ZeshuLiu/esp32_keyboard/Keyboard_code/poker_keyboard/poker_keyboard.h

#ifndef ESP_KEYBOARD_H
#define ESP_KEYBOARD_H
#include "Layout.h"
#include "L_CH932x.h"

bool DBG_KEYBOARD = 1;

#ifdef Joker
# define DeviceName "Joker_60" //设备名
#endif

#ifdef MasterYoda
# define DeviceName "MasterYoda"
#endif

# define Manufacturer "Liu"        //设备制造商
# define DevicePower 100             //电量

int DFT_BOOT_MODE; //0是usb，1是蓝牙


//I2C总线信息
# define kbd_SDA 21
# define kbd_SCL 22

#ifdef Joker
#ifdef Ver2
L_CH9329 ch9329;
#endif
#endif


#endif
