ZeshuLiu/esp32_keyboard/Keyboard_code/poker_keyboard/Pic.h

static const unsigned char dog_bmp [] PROGMEM ={
0xFF,0xFF,0xFF,0xFF,0xFF,0xFF,0xFF,0xFF,0xFF,0xFF,0xFF,0xFF,0xFF,0xFF,0xFF,0xFF,
0xFF,0xFF,0xFF,0xFF,0xFF,0xFF,0xFF,0xFF,0xFF,0xFF,0xFF,0xFF,0xFF,0xFF,0xFF,0xFF,
0xFF,0xFF,0xFF,0xFF,0xFF,0xFF,0xFF,0xFF,0x09,0x00,0xFF,0xFF,0xFF,0xFF,0xFF,0xFF,
0xFF,0xFF,0xFF,0xFF,0xFF,0xFF,0xFF,0x3F,0x1F,0x00,0xF0,0xFF,0xFF,0xFF,0xFF,0xFF,
0xFF,0xFF,0xFF,0xFF,0xFF,0xFF,0xFF,0xC3,0xFF,0xFF,0xC2,0xFF,0xFF,0xFF,0xFF,0xFF,
0xFF,0xFF,0xFF,0xFF,0xFF,0xFF,0x7F,0xF8,0xFF,0xFF,0x0F,0xFF,0xFF,0xFF,0xFF,0xFF,
0xFF,0xFF,0xFF,0xFF,0xFF,0xFF,0x0F,0xFC,0xFF,0xFF,0x3F,0xFC,0xFF,0xFF,0xFF,0xFF,
0xFF,0xFF,0xFF,0xFF,0xFF,0xFF,0x07,0xFE,0xFF,0xFF,0xFF,0xF8,0xFF,0xFF,0xFF,0xFF,
0xFF,0xFF,0xFF,0xFF,0xFF,0xFF,0x27,0xFF,0xFF,0xFA,0xFF,0xC1,0xFF,0xFF,0xFF,0xFF,
0xFF,0xFF,0xFF,0xFF,0xFF,0xFF,0x93,0x7F,0x7F,0xF8,0xFF,0x87,0xFF,0xFF,0xFF,0xFF,
0xFF,0xFF,0xFF,0xFF,0xFF,0xFF,0xB3,0x7F,0x78,0xFC,0xFF,0x3D,0xFF,0xFF,0xFF,0xFF,
0xFF,0xFF,0xFF,0xFF,0xFF,0xFF,0x19,0x1F,0x7E,0xFE,0x9F,0x39,0xFF,0xFF,0xFF,0xFF,
0xFF,0xFF,0xFF,0xFF,0xFF,0xFF,0x09,0x5E,0x7C,0xF8,0x1F,0x20,0xFE,0xFF,0xFF,0xFF,
0xFF,0xFF,0xFF,0xFF,0xFF,0xFF,0xDD,0xDF,0x3E,0xC0,0x31,0xE0,0xFC,0xFF,0xFF,0xFF,
0xFF,0xFF,0xFF,0xFF,0xFF,0xFF,0xE6,0xFB,0x3F,0x00,0xE1,0xC0,0xE1,0xFF,0xFF,0xFF,
0xFF,0xFF,0xFF,0xFF,0xFF,0x7F,0x26,0xF8,0x3F,0x00,0xE0,0xF8,0xE3,0xFF,0xFF,0xFF,
0xFF,0xFF,0xFF,0xFF,0xFF,0x7F,0x17,0xFC,0x7F,0x00,0x30,0xE0,0xC7,0xFF,0xFF,0xFF,
0xFF,0xFF,0xFF,0xFF,0xFF,0x9F,0x17,0xF8,0xFF,0x40,0x31,0xCE,0x0F,0xFF,0xFF,0xFF,
0xFF,0xFF,0xFF,0xFF,0xFF,0x8F,0x23,0xC6,0xFF,0xF1,0x38,0xFC,0x3F,0xFC,0xFF,0xFF,
0xFF,0xFF,0xFF,0xFF,0xFF,0xDF,0xE7,0x81,0xFF,0xFF,0x10,0xFD,0x5F,0xF0,0xFF,0xFF,
0xFF,0xFF,0xFF,0xFF,0xFF,0xDF,0xE3,0x88,0xFF,0x7F,0x1E,0xFF,0x87,0xFF,0xFF,0xFF,
0xFF,0xFF,0xFF,0xFF,0xFF,0xCF,0x23,0x3E,0xFF,0x7F,0x3E,0xFE,0x1F,0xFE,0xFF,0xFF,
0xFF,0xFF,0xFF,0xFF,0xFF,0xCF,0x83,0x3F,0xFF,0x3F,0x1F,0xFC,0x3F,0xFF,0xFF,0xFF,
0xFF,0xFF,0xFF,0xFF,0xFF,0xCF,0xC3,0x69,0xFE,0x3F,0xBF,0xFD,0x7F,0xFE,0xFF,0xFF,
0xFF,0xFF,0xFF,0xFF,0xFF,0xE7,0x37,0xC0,0xFC,0xFF,0x1F,0xFF,0x3F,0xFF,0xFF,0xFF,
0xFF,0xFF,0xFF,0xFF,0xFF,0xC3,0x17,0x80,0xFF,0xFF,0x3F,0xFF,0x3F,0xFF,0xFF,0xFF,
0xFF,0xFF,0xFF,0xFF,0xFF,0xCB,0x87,0x07,0x7F,0xFF,0x9F,0xFF,0x8F,0xFF,0xFF,0xFF,
0xFF,0xFF,0xFF,0xFF,0xFF,0xCF,0xC7,0x15,0x7E,0xFE,0x8F,0xFF,0xCF,0xFF,0xFF,0xFF,
0xFF,0xFF,0xFF,0xFF,0xFF,0xC7,0x07,0x01,0xBF,0xFE,0xA7,0xFF,0xE3,0xFF,0xFF,0xFF,
0xFF,0xFF,0xFF,0xFF,0xFF,0xEF,0x07,0x00,0x7E,0xFC,0x9F,0xFF,0xF3,0xFF,0xFF,0xFF,
0xFF,0xFF,0xFF,0xFF,0xFF,0x1F,0x06,0x00,0x7F,0xFA,0xFF,0xFF,0xFB,0xFF,0xFF,0xFF,
0xFF,0xFF,0xFF,0xFF,0xFF,0x1F,0x1B,0x14,0xFF,0xFE,0xFF,0xFF,0xF9,0xFF,0xFF,0xFF,
0xFF,0xFF,0xFF,0xFF,0xFF,0x6F,0x97,0x88,0x7F,0xFC,0xFF,0x7F,0xFE,0xFF,0xFF,0xFF,
0xFF,0xFF,0xFF,0xFF,0xFF,0x7F,0x3B,0x00,0xFF,0xFC,0xFB,0x7F,0xFC,0xFF,0xFF,0xFF,
0xFF,0xFF,0xFF,0xFF,0xFF,0xFF,0x76,0x80,0x7F,0xFE,0xFD,0xFF,0xFC,0xFF,0xFF,0xFF,
0xFF,0xFF,0xFF,0xFF,0xFF,0xFF,0x76,0x00,0xFF,0xFE,0xF9,0xEF,0xFC,0xFF,0xFF,0xFF,
0xFF,0xFF,0xFF,0xFF,0xFF,0xFF,0xFE,0x00,0xFF,0xFE,0xE4,0xF3,0xF8,0xFF,0xFF,0xFF,
0xFF,0xFF,0xFF,0xFF,0xFF,0xFF,0x74,0x08,0xFF,0xFF,0x1C,0x30,0xFC,0xFF,0xFF,0xFF,
0xFF,0xFF,0xFF,0xFF,0xFF,0xFF,0x70,0x34,0xFE,0x3F,0x1E,0xB0,0xFE,0xFF,0xFF,0xFF,
0xFF,0xFF,0xFF,0xFF,0xFF,0x7F,0x70,0xC2,0xFC,0x1F,0x4E,0x0E,0xFE,0xFF,0xFF,0xFF,
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
